Rubiks-boy/ORBD/Data and Visuals/travel time v num chars.png

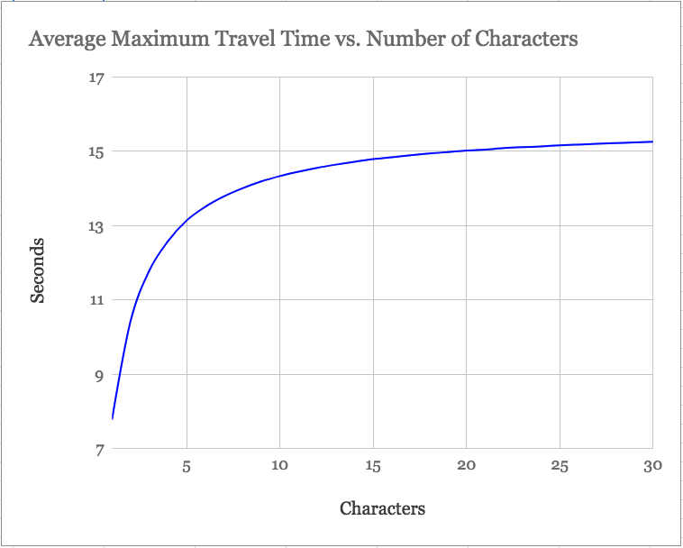
Data and Visuals/travel time v num chars.png
